Protocentral/protocentral_sensything/docs/images/brain-pipeline.jpg

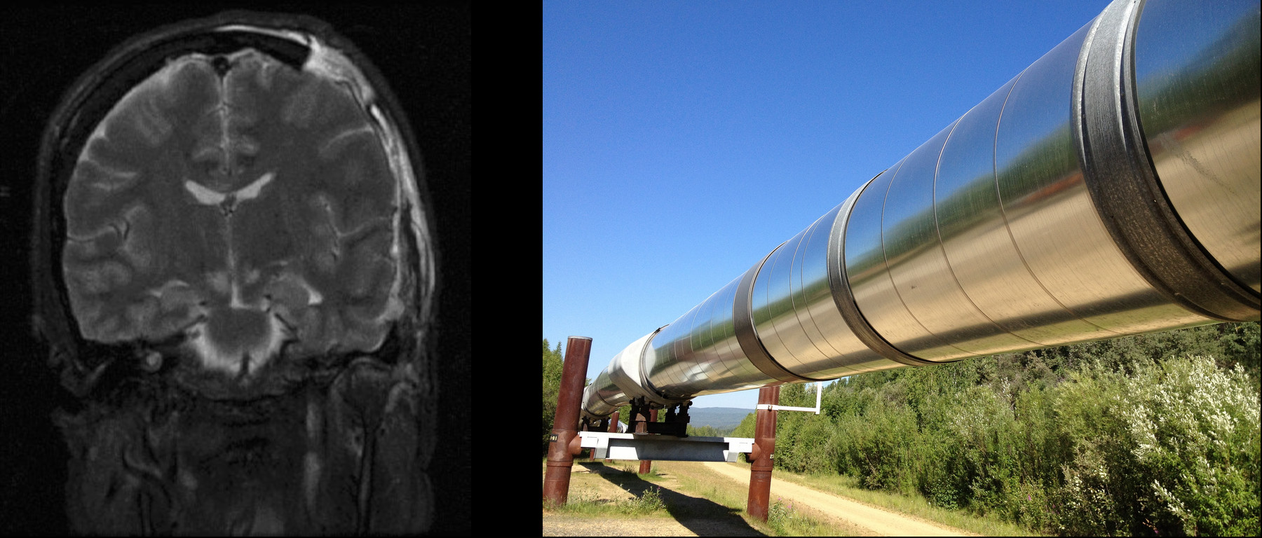
docs/images/brain-pipeline.jpg
