Protocentral/protocentral_sensything/docs/images/curious.jpg

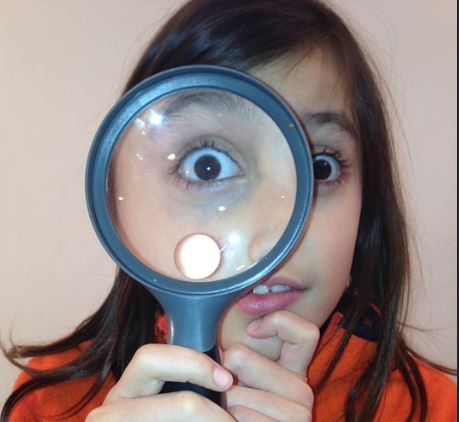
docs/images/curious.jpg
