Protocentral/protocentral_sensything/docs/images/Datalog.JPG

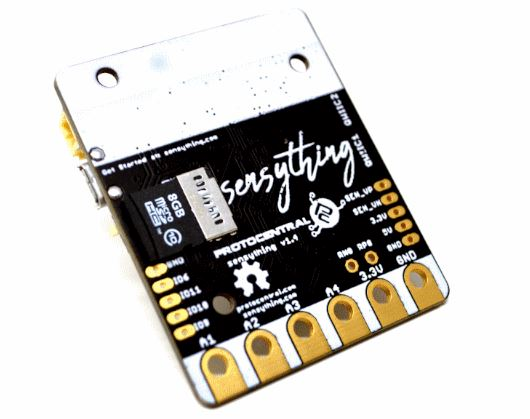
docs/images/Datalog.JPG
