Protocentral/protocentral_sensything/docs/images/Developer mode image.JPG

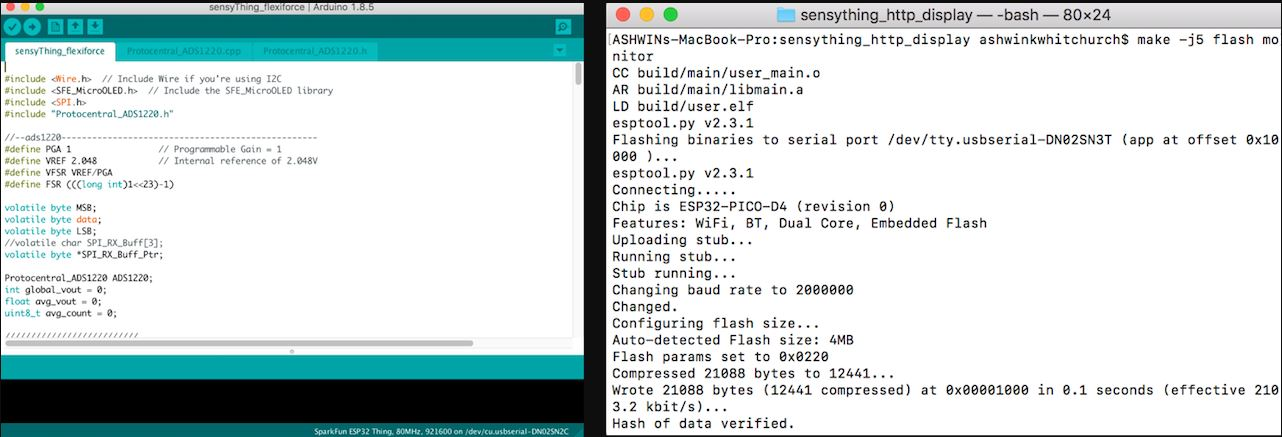
docs/images/Developer mode image.JPG
