Protocentral/protocentral_sensything/docs/images/forest.jpg

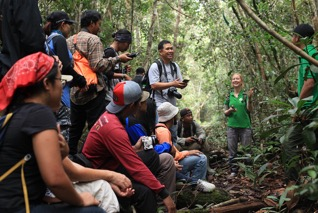
docs/images/forest.jpg
