Protocentral/protocentral_sensything/docs/images/Highlights.jpg

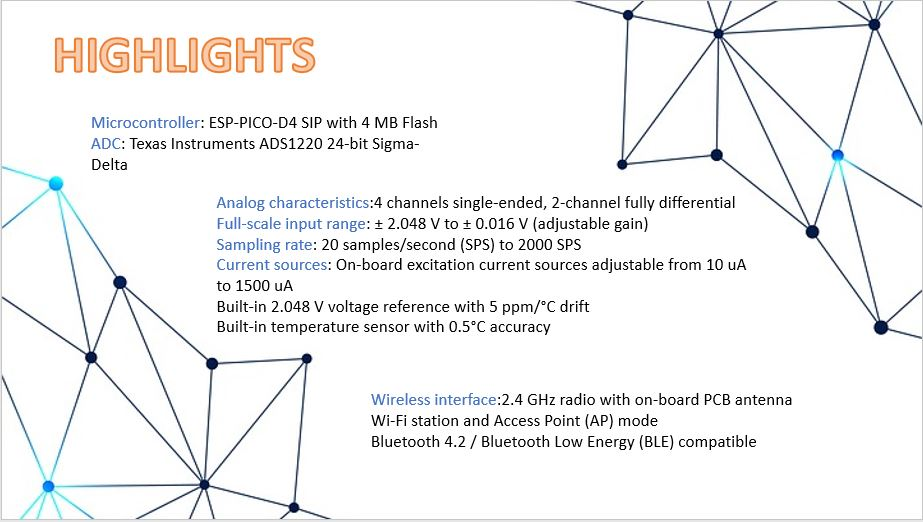
docs/images/Highlights.jpg
