Protocentral/protocentral_sensything/docs/images/openpressure.jpg

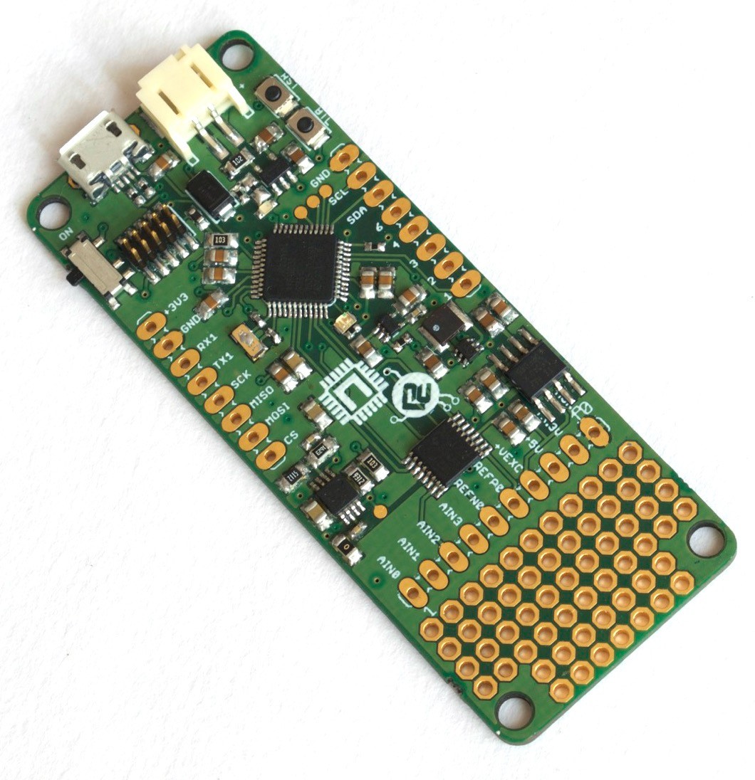
docs/images/openpressure.jpg
