Protocentral/protocentral_sensything/docs/images/protect-the-world.jpg

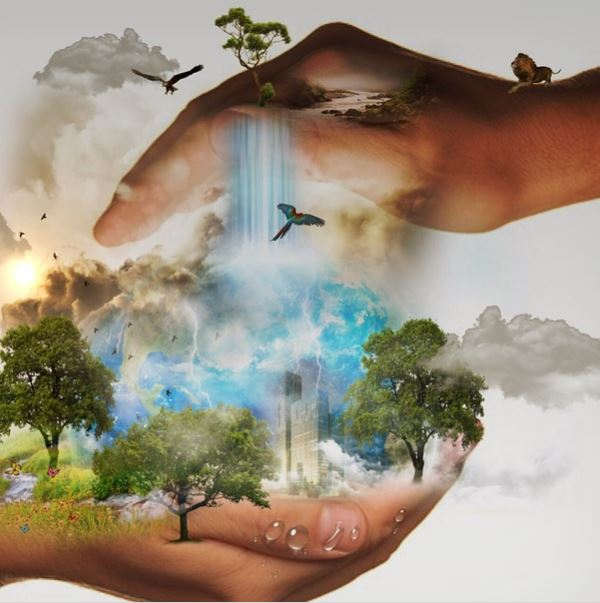
docs/images/protect-the-world.jpg
