Protocentral/protocentral_sensything/docs/images/Read include.png

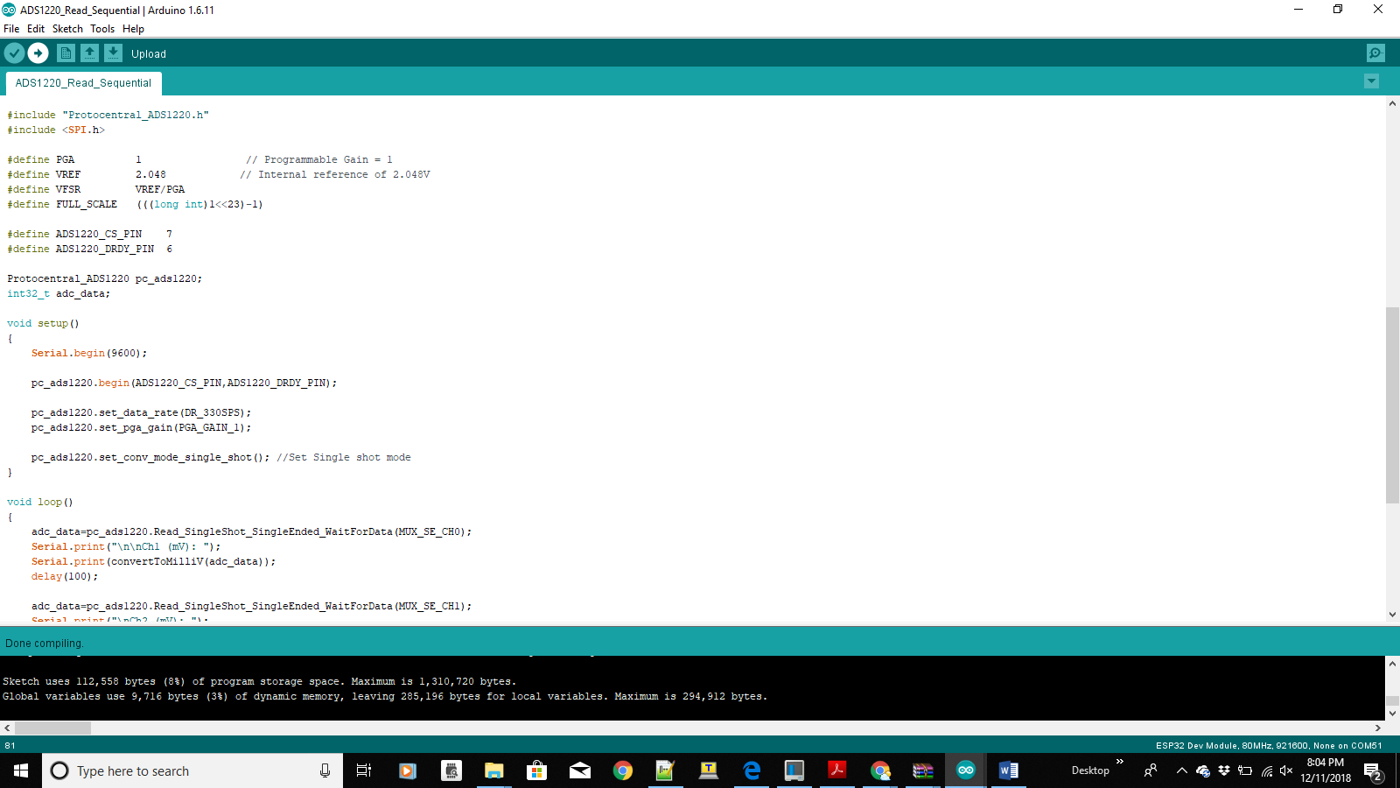
docs/images/Read include.png
