Protocentral/protocentral_sensything/docs/images/Sensything main image.jpg

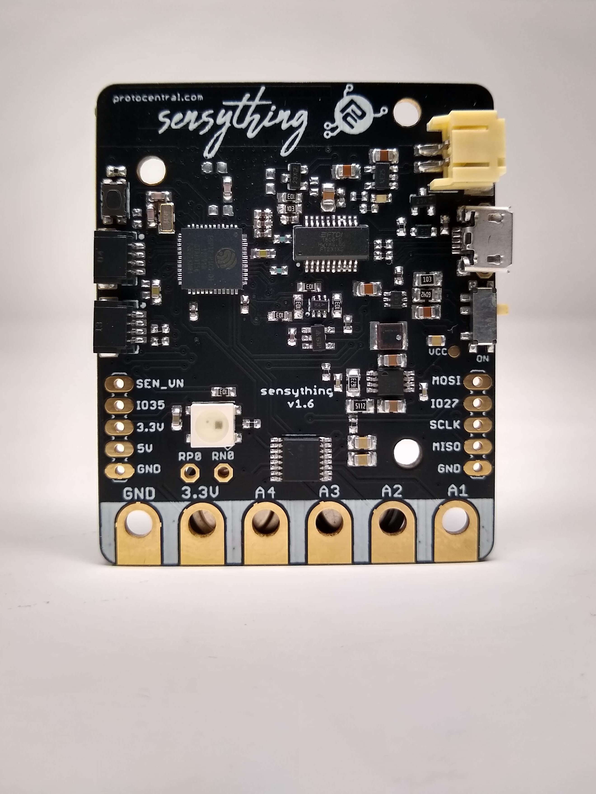
docs/images/Sensything main image.jpg
