Protocentral/protocentral_sensything/docs/images/Sensything main.jpg

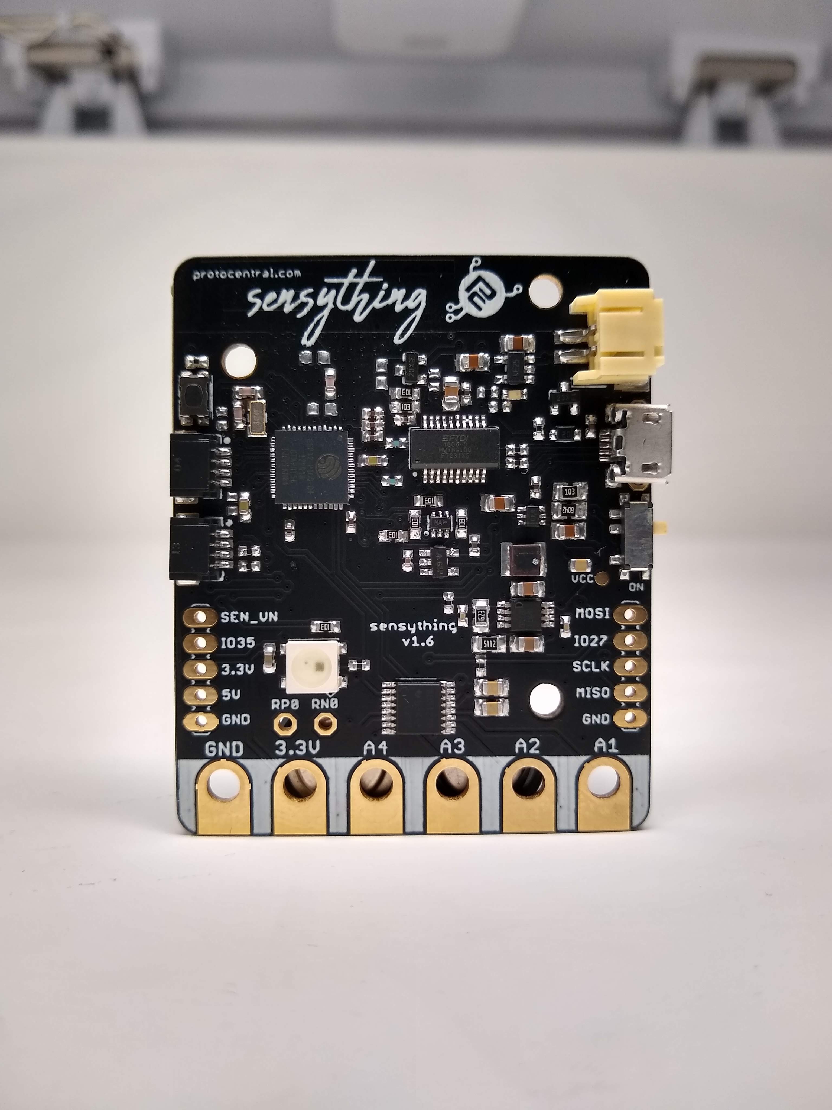
docs/images/Sensything main.jpg
