Protocentral/protocentral_sensything/docs/images/sensything-5-pack.jpg

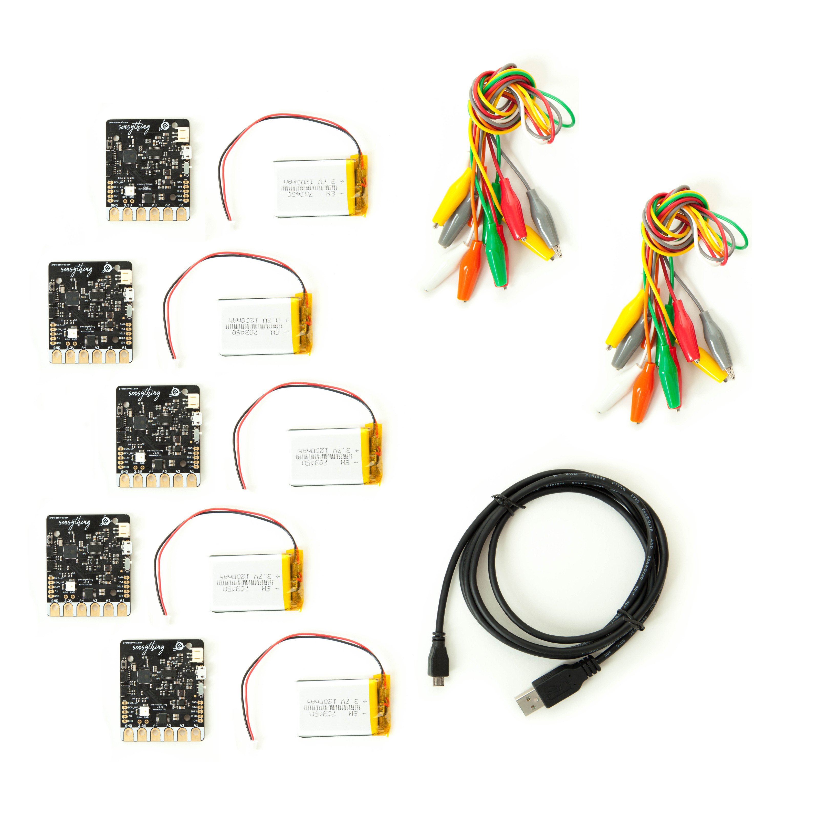
docs/images/sensything-5-pack.jpg
