Protocentral/protocentral_sensything/docs/images/sensything-16.jpg

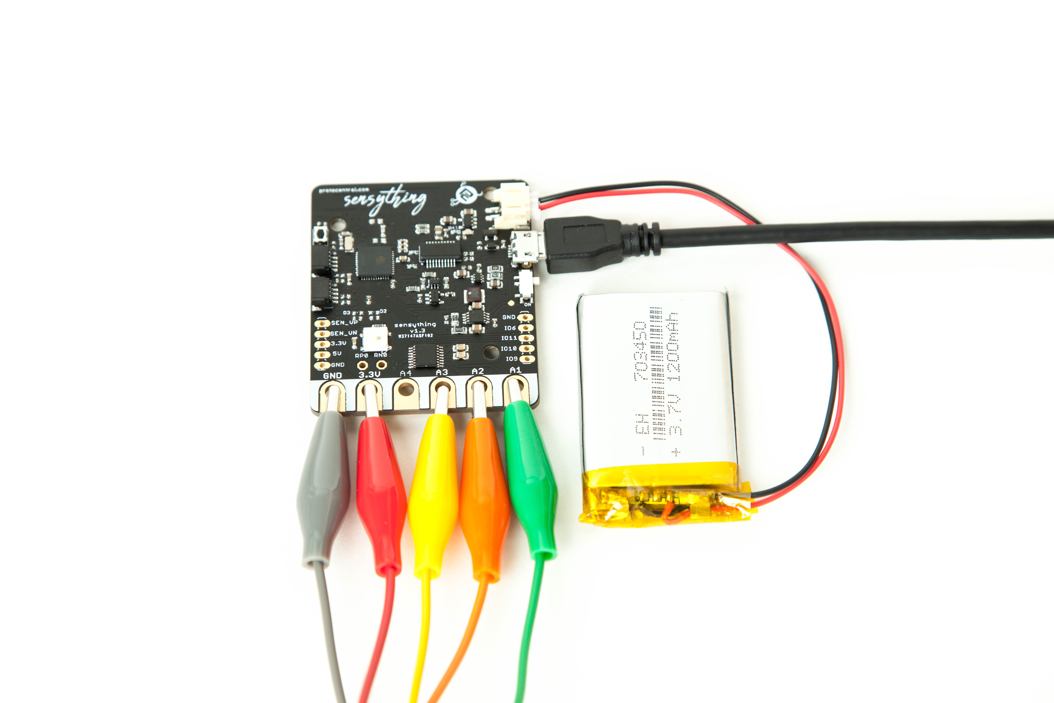
docs/images/sensything-16.jpg
