Protocentral/protocentral_sensything/docs/images/sensything-battery-2.jpg

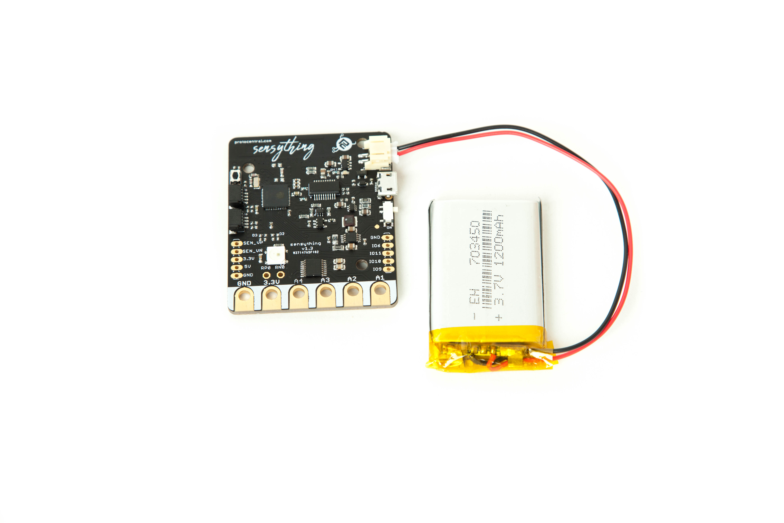
docs/images/sensything-battery-2.jpg
