Protocentral/protocentral_sensything/docs/images/sensything-battery-usb.jpg

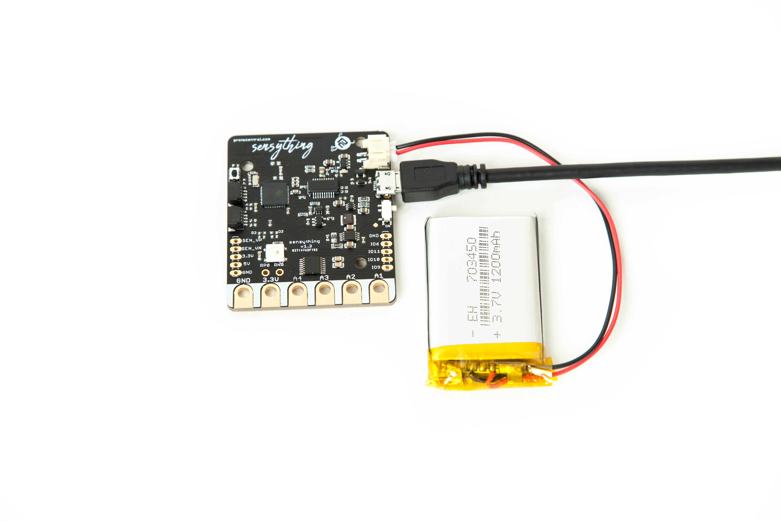
docs/images/sensything-battery-usb.jpg
