Protocentral/protocentral_sensything/docs/images/sensything-battery.jpg

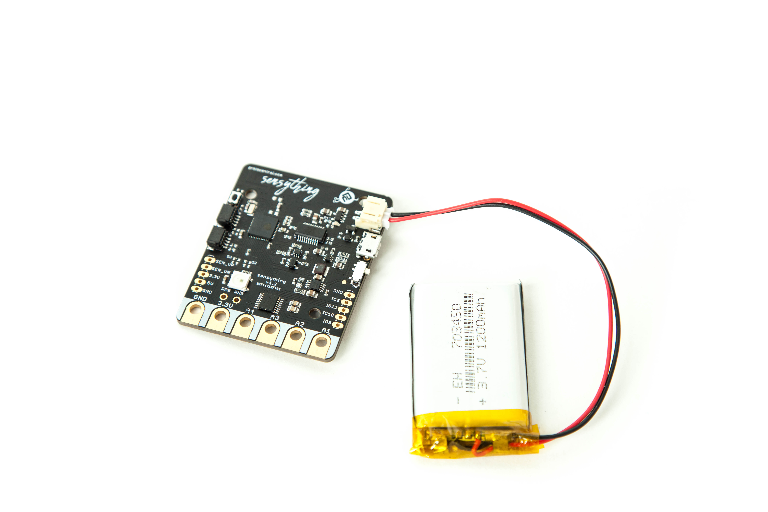
docs/images/sensything-battery.jpg
