Protocentral/protocentral_sensything/docs/images/sensything-bottom.jpg

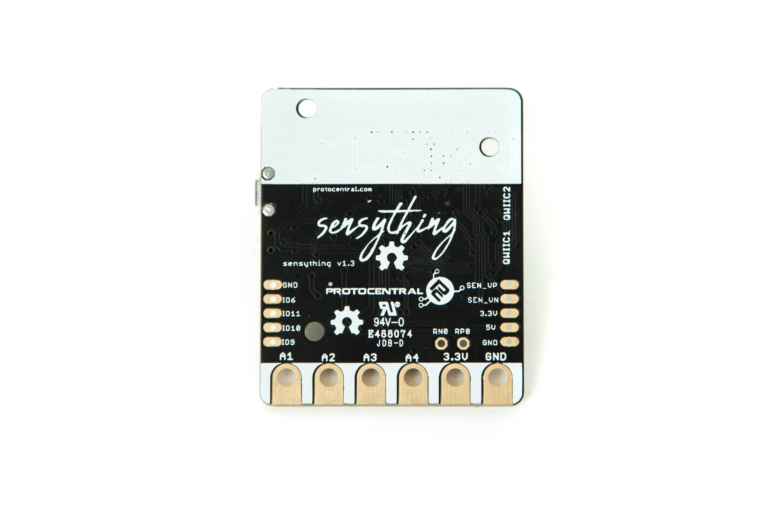
docs/images/sensything-bottom.jpg
