Protocentral/protocentral_sensything/docs/images/sensything-iso.jpg

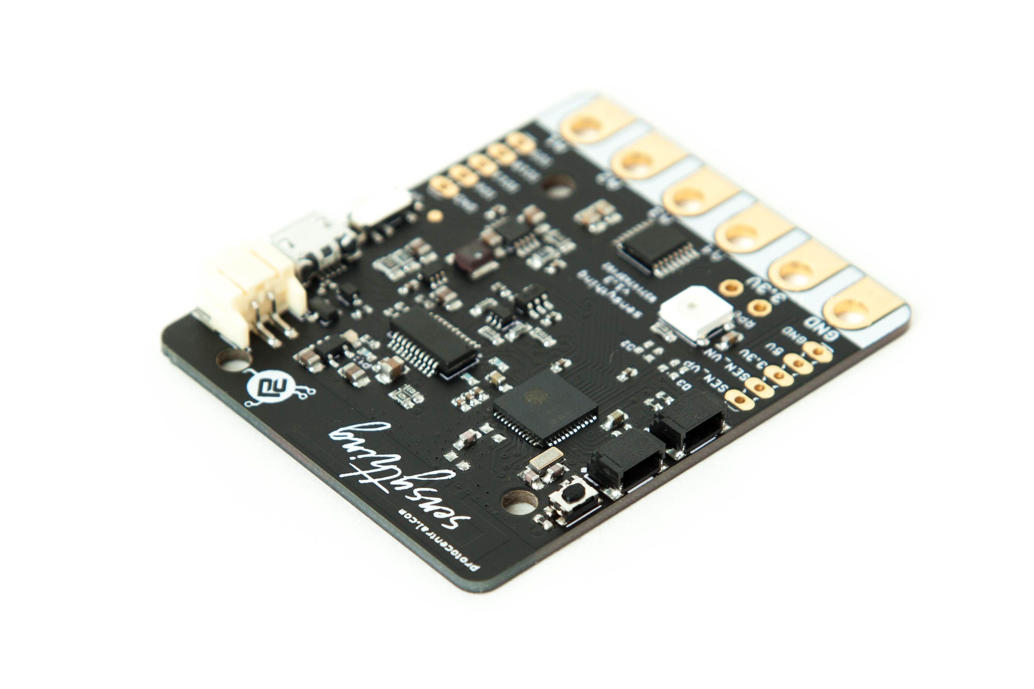
docs/images/sensything-iso.jpg
