Protocentral/protocentral_sensything/docs/images/sensything-microsd.jpg

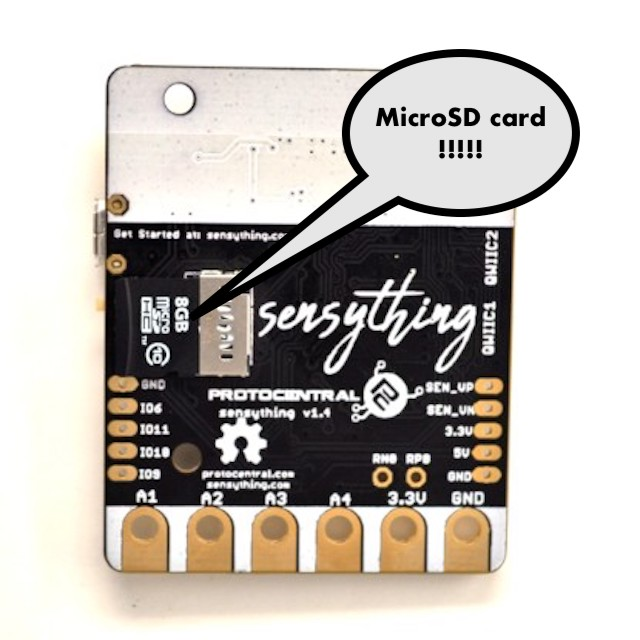
docs/images/sensything-microsd.jpg
