Protocentral/protocentral_sensything/docs/images/sensything-protos.jpg

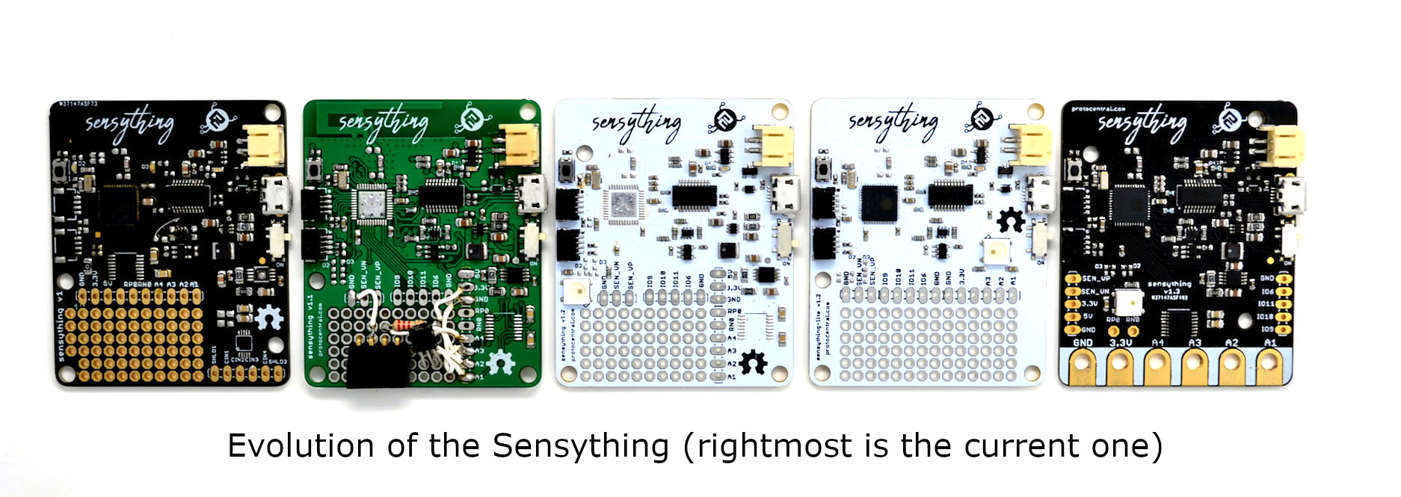
docs/images/sensything-protos.jpg
