Protocentral/protocentral_sensything/docs/images/sensything-shot-sept-26.jpg

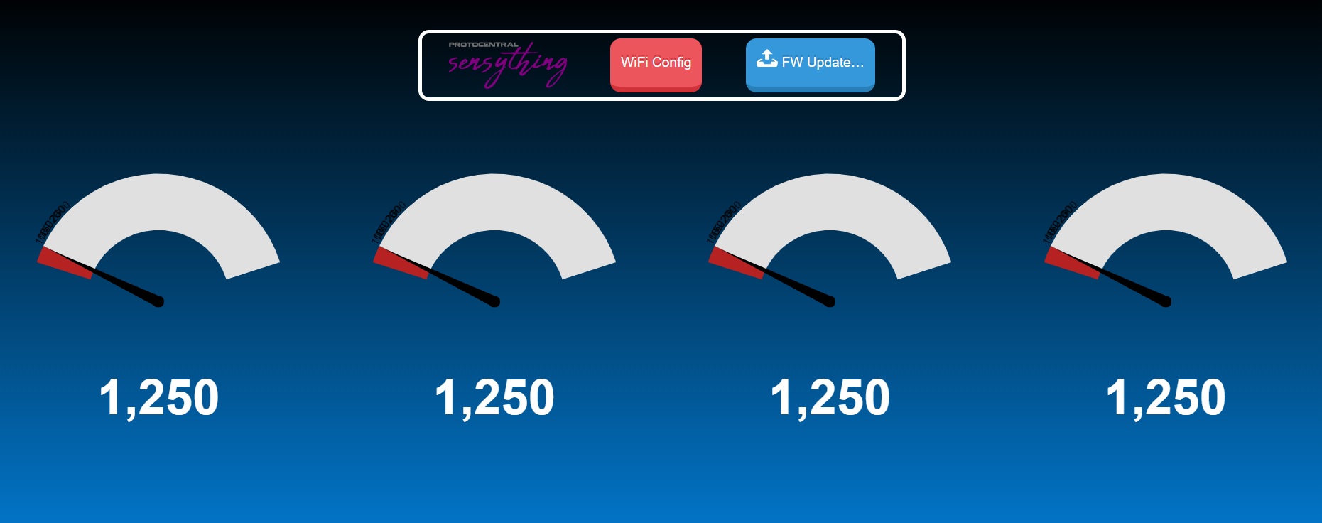
docs/images/sensything-shot-sept-26.jpg
