Protocentral/protocentral_sensything/docs/images/sensything-solo-pledge.jpg

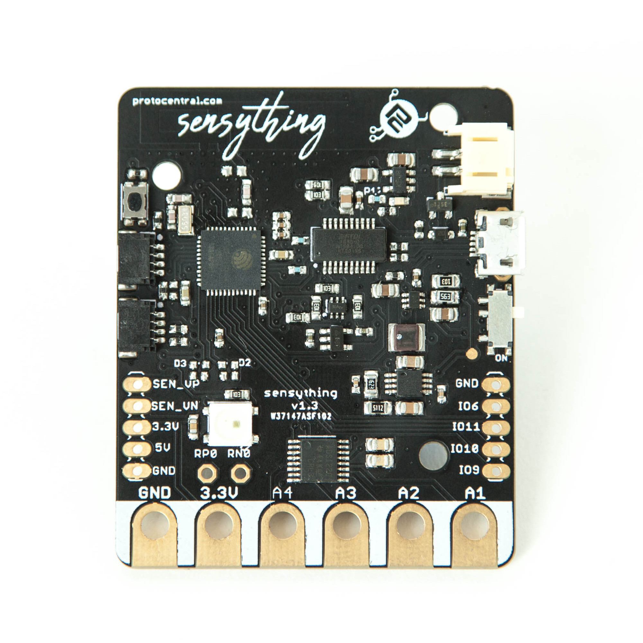
docs/images/sensything-solo-pledge.jpg
