Protocentral/protocentral_sensything/docs/images/sensything-solo.jpg

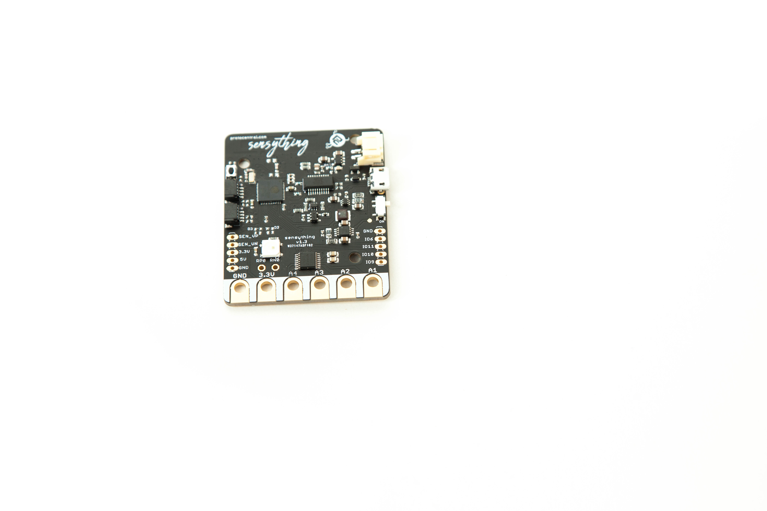
docs/images/sensything-solo.jpg
