Protocentral/protocentral_sensything/docs/images/sensything-top-iso.jpg

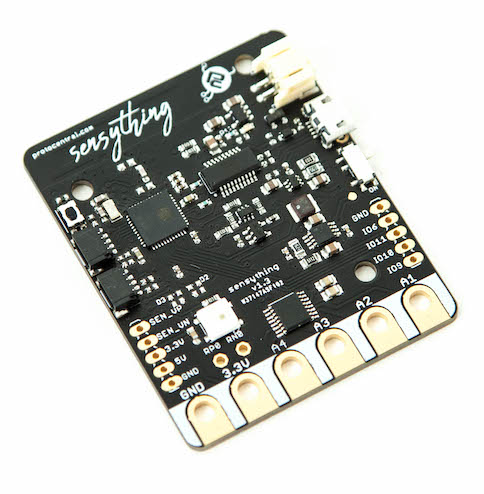
docs/images/sensything-top-iso.jpg
