Protocentral/protocentral_sensything/docs/images/sensything-top-NAMED.jpg

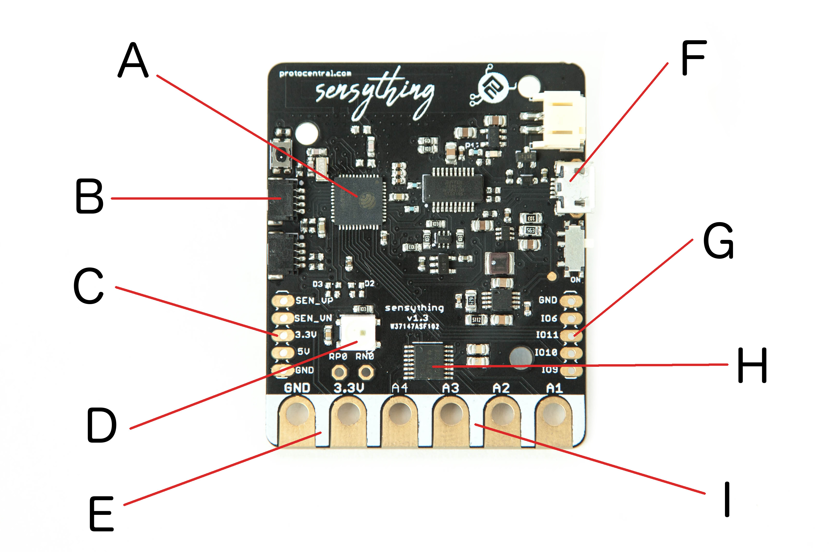
docs/images/sensything-top-NAMED.jpg
