Protocentral/protocentral_sensything/docs/images/sensything-top.jpg

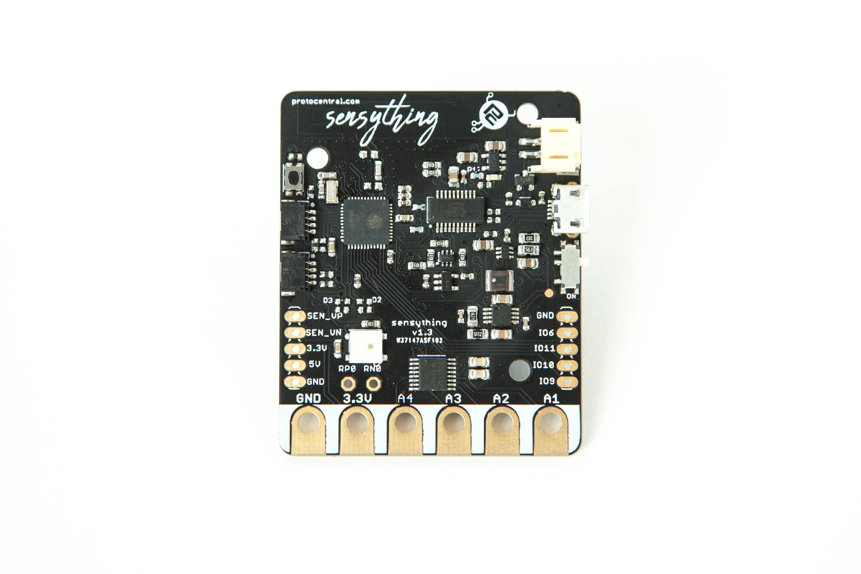
docs/images/sensything-top.jpg
