Protocentral/protocentral_sensything/docs/images/sensything-usb.jpg

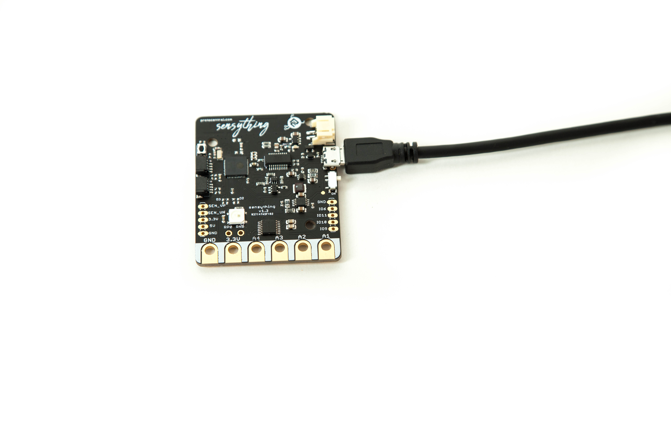
docs/images/sensything-usb.jpg
