Protocentral/protocentral_sensything/docs/images/sensything-with-app-clean.jpg

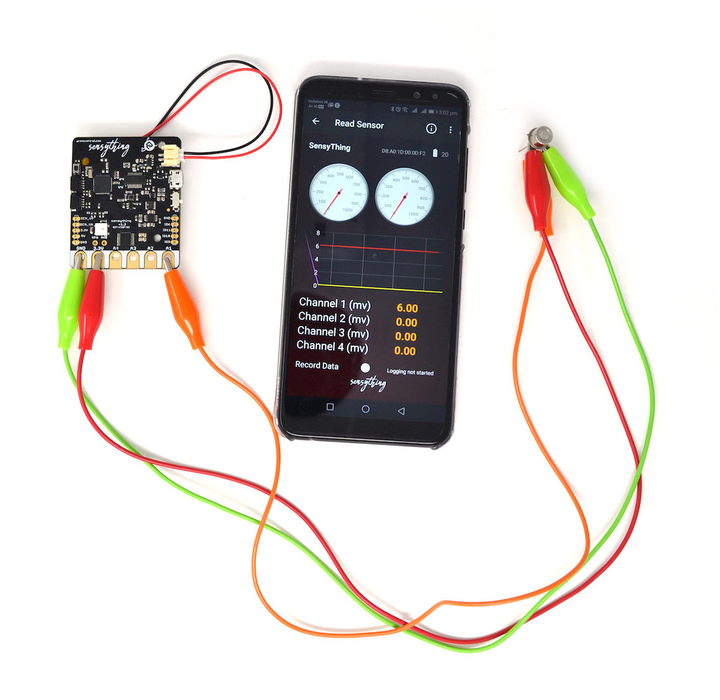
docs/images/sensything-with-app-clean.jpg
