Protocentral/protocentral_sensything/docs/images/sensything-with-app.jpg

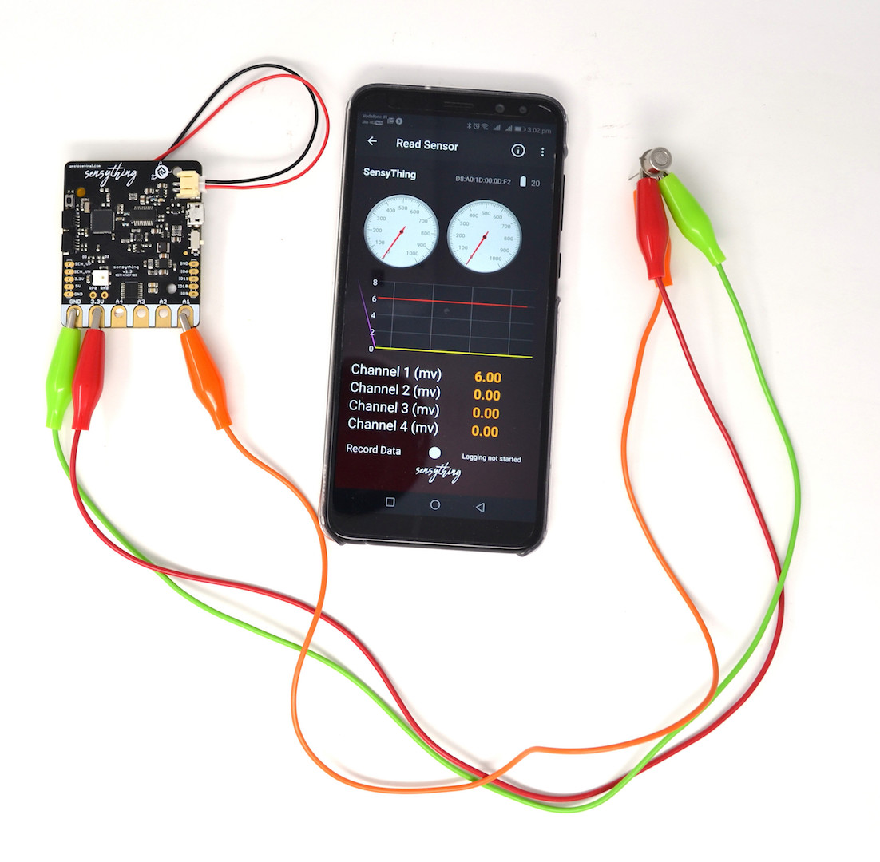
docs/images/sensything-with-app.jpg
