Protocentral/protocentral_sensything/docs/images/sensything-with-sensor.jpg

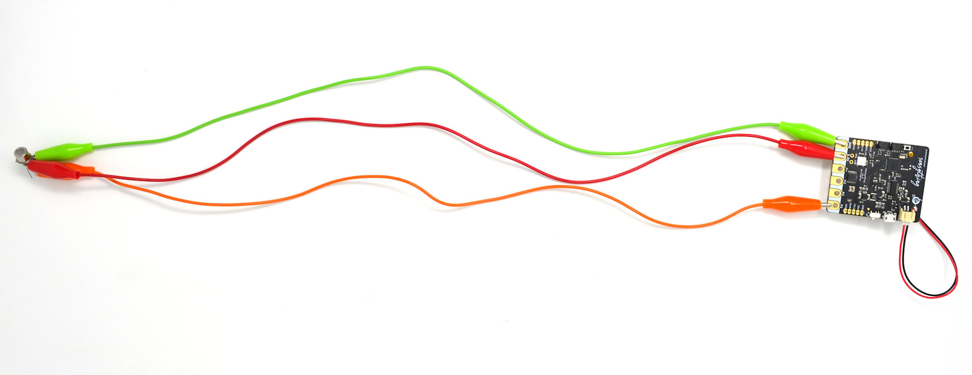
docs/images/sensything-with-sensor.jpg
