Protocentral/protocentral_sensything/docs/images/sensything_prelaunch.jpg

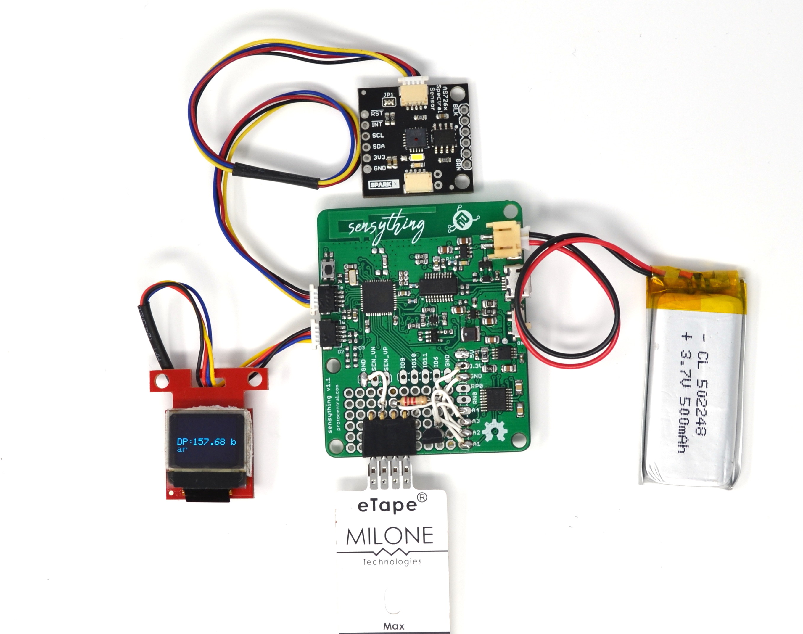
docs/images/sensything_prelaunch.jpg
