Protocentral/protocentral_sensything/docs/images/sensything_qwiic_diagram.png

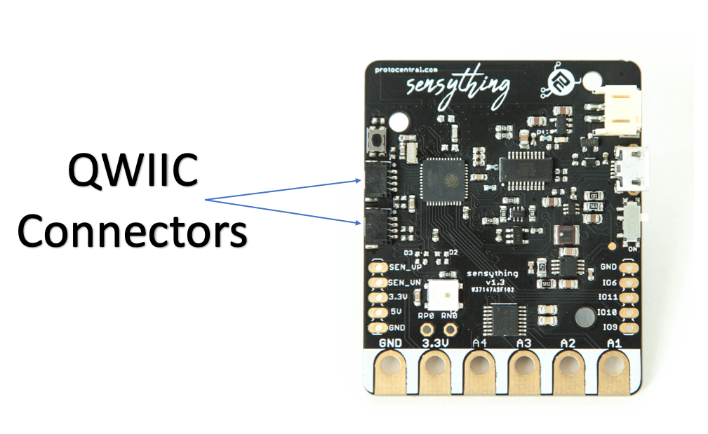
docs/images/sensything_qwiic_diagram.png
