Protocentral/protocentral_sensything/docs/images/signal-adc.png

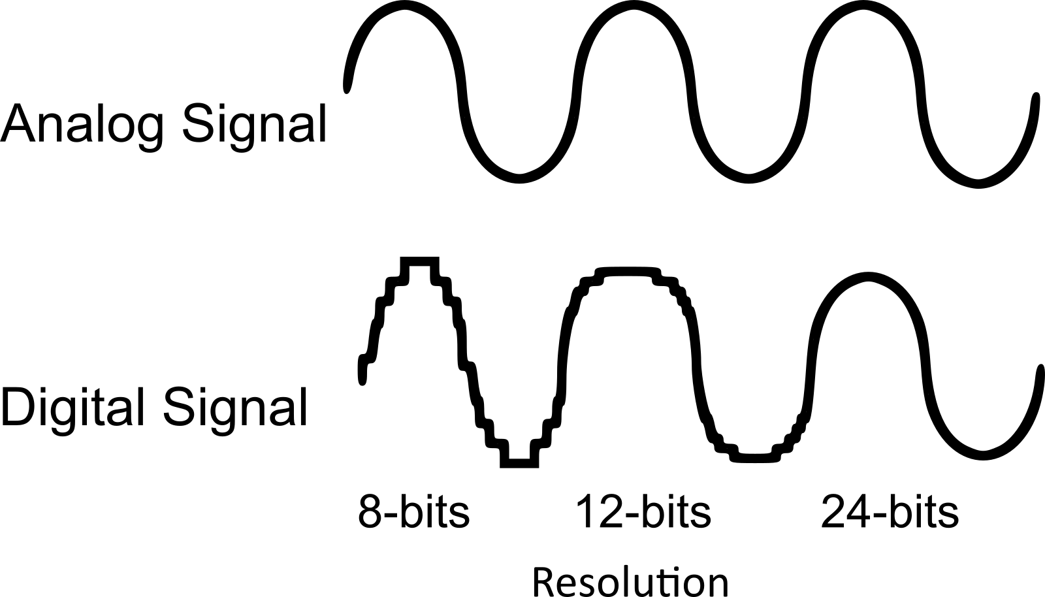
docs/images/signal-adc.png
