Protocentral/protocentral_sensything/docs/images/tree.jpg

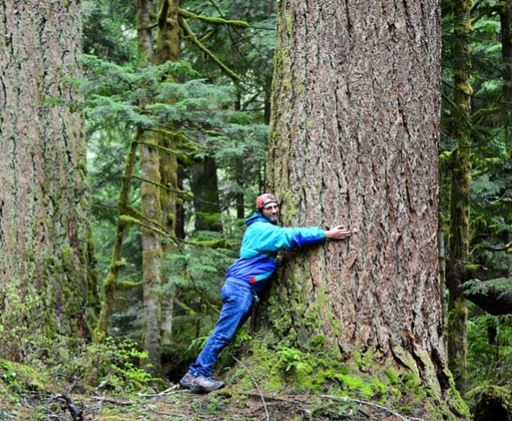
docs/images/tree.jpg
