Protocentral/protocentral_sensything/software/Sensything_esp-idf/Sensything_experiments/Qwiic_Sensors/activity_classifier/components/libesphttpd/util/captdns.c

/* This Source Code Form is subject to the terms of the Mozilla Public
 * License, v. 2.0. If a copy of the MPL was not distributed with this
 * file, You can obtain one at http://mozilla.org/MPL/2.0/. */


/*
This is a 'captive portal' DNS server: it basically replies with a fixed IP (in this case:
the one of the SoftAP interface of this ESP module) for any and all DNS queries. This can
be used to send mobile phones, tablets etc which connect to the ESP in AP mode directly to
the internal webserver.
*/

#include <libesphttpd/esp.h>
#include "esp_log.h"

static const char* TAG = "captdns";

#ifdef FREERTOS

#ifdef ESP32
#include "freertos/FreeRTOS.h"
#include "freertos/task.h"
#include "freertos/queue.h"
#include "tcpip_adapter.h"
#else
#include "FreeRTOS.h"
#include "task.h"
#include "queue.h"
#endif


#include "lwip/sockets.h"
#include "lwip/err.h"
static int sockFd;
#endif


#define DNS_LEN 512

typedef struct __attribute__ ((packed)) {
	uint16_t id;
	uint8_t flags;
	uint8_t rcode;
	uint16_t qdcount;
	uint16_t ancount;
	uint16_t nscount;
	uint16_t arcount;
} DnsHeader;


typedef struct __attribute__ ((packed)) {
	uint8_t len;
	uint8_t data;
} DnsLabel;


typedef struct __attribute__ ((packed)) {
	//before: label
	uint16_t type;
	uint16_t class;
} DnsQuestionFooter;


typedef struct __attribute__ ((packed)) {
	//before: label
	uint16_t type;
	uint16_t class;
	uint32_t ttl;
	uint16_t rdlength;
	//after: rdata
} DnsResourceFooter;

typedef struct __attribute__ ((packed)) {
	uint16_t prio;
	uint16_t weight;
} DnsUriHdr;


#define FLAG_QR (1<<7)
#define FLAG_AA (1<<2)
#define FLAG_TC (1<<1)
#define FLAG_RD (1<<0)

#define QTYPE_A  1
#define QTYPE_NS 2
#define QTYPE_CNAME 5
#define QTYPE_SOA 6
#define QTYPE_WKS 11
#define QTYPE_PTR 12
#define QTYPE_HINFO 13
#define QTYPE_MINFO 14
#define QTYPE_MX 15
#define QTYPE_TXT 16
#define QTYPE_URI 256

#define QCLASS_IN 1
#define QCLASS_ANY 255
#define QCLASS_URI 256


//Function to put unaligned 16-bit network values
static void ICACHE_FLASH_ATTR setn16(void *pp, int16_t n) {
	char *p=pp;
	*p++=(n>>8);
	*p++=(n&0xff);
}

//Function to put unaligned 32-bit network values
static void ICACHE_FLASH_ATTR setn32(void *pp, int32_t n) {
	char *p=pp;
	*p++=(n>>24)&0xff;
	*p++=(n>>16)&0xff;
	*p++=(n>>8)&0xff;
	*p++=(n&0xff);
}

//Parses a label into a C-string containing a dotted
//Returns pointer to start of next fields in packet
static char* ICACHE_FLASH_ATTR labelToStr(char *packet, char *labelPtr, int packetSz, char *res, int resMaxLen) {
	int i, j, k;
	char *endPtr=NULL;
	i=0;
	do {
		if ((*labelPtr&0xC0)==0) {
			j=*labelPtr++; //skip past length
			//Add separator period if there already is data in res
			if (i<resMaxLen && i!=0) res[i++]='.';
			//Copy label to res
			for (k=0; k<j; k++) {
				if ((labelPtr-packet)>packetSz) return NULL;
				if (i<resMaxLen) res[i++]=*labelPtr++;
			}
		} else if ((*labelPtr&0xC0)==0xC0) {
			//Compressed label pointer
			endPtr=labelPtr+2;
			int offset=ntohs(*((uint16_t *)labelPtr))&0x3FFF;
			//Check if offset points to somewhere outside of the packet
			if (offset>packetSz) return NULL;
			labelPtr=&packet[offset];
		}
		//check for out-of-bound-ness
		if ((labelPtr-packet)>packetSz) return NULL;
	} while (*labelPtr!=0);
	res[i]=0; //zero-terminate
	if (endPtr==NULL) endPtr=labelPtr+1;
	return endPtr;
}


//Converts a dotted hostname to the weird label form dns uses.
static char ICACHE_FLASH_ATTR *strToLabel(char *str, char *label, int maxLen) {
	char *len=label; //ptr to len byte
	char *p=label+1; //ptr to next label byte to be written
	while (1) {
		if (*str=='.' || *str==0) {
			*len=((p-len)-1);	//write len of label bit
			len=p;				//pos of len for next part
			p++;				//data ptr is one past len
			if (*str==0) break;	//done
			str++;
		} else {
			*p++=*str++;	//copy byte
//			if ((p-label)>maxLen) return NULL;	//check out of bounds
		}
	}
	*len=0;
	return p; //ptr to first free byte in resp
}


//Receive a DNS packet and maybe send a response back
static char buff[DNS_LEN];
static char reply[DNS_LEN];

#ifndef FREERTOS
static void ICACHE_FLASH_ATTR captdnsRecv(void* arg, char *pusrdata, unsigned short length) {
	struct espconn *conn=(struct espconn *)arg;
#else
static void ICACHE_FLASH_ATTR captdnsRecv(struct sockaddr_in *premote_addr, char *pusrdata, unsigned short length) {
#endif
	int i;
	char *rend=&reply[length];
	char *p=pusrdata;
	DnsHeader *hdr=(DnsHeader*)p;
	DnsHeader *rhdr=(DnsHeader*)&reply[0];
	p+=sizeof(DnsHeader);
    ESP_LOGD(TAG, "DNS packet: id 0x%X flags 0x%X rcode 0x%X qcnt %d ancnt %d nscount %d arcount %d len %d",
		ntohs(hdr->id), hdr->flags, hdr->rcode, ntohs(hdr->qdcount), ntohs(hdr->ancount), ntohs(hdr->nscount), ntohs(hdr->arcount), length);
    //Some sanity checks:
    if (length>DNS_LEN) // Packet is longer than DNS implementation allows
    {
        ESP_LOGD(TAG, "Packet length %d longer than DNS_LEN(%d)", length, DNS_LEN);
        return;
    }
	if (length<sizeof(DnsHeader)) // Packet is too short
    {
        ESP_LOGD(TAG, "Packet length %d shorter than %d", length, sizeof(DnsHeader));
        return;
    }
    // NOTE: We are ok if hdr->arcount is non-zero as these could be extension
    // records, but we don't process them
	if (hdr->ancount || hdr->nscount) //this is a reply, don't know what to do with it
    {
        ESP_LOGD(TAG, "Ignoring reply");
        return;
    }

    if (hdr->flags&FLAG_TC) //truncated, can't use this
    {
        ESP_LOGD(TAG, "Message truncated");
        return;
    }

	//Reply is basically the request plus the needed data
	memcpy(reply, pusrdata, length);
	rhdr->flags|=FLAG_QR;
	for (i=0; i<ntohs(hdr->qdcount); i++) {
		//Grab the labels in the q string
		p=labelToStr(pusrdata, p, length, buff, sizeof(buff));
		if (p==NULL) return;
		DnsQuestionFooter *qf=(DnsQuestionFooter*)p;
		p+=sizeof(DnsQuestionFooter);
		ESP_LOGI(TAG, "DNS: Q (type 0x%X class 0x%X) for %s", ntohs(qf->type), ntohs(qf->class), buff);
		if (ntohs(qf->type)==QTYPE_A) {
			//They want to know the IPv4 address of something.
			//Build the response.
			rend=strToLabel(buff, rend, sizeof(reply)-(rend-reply)); //Add the label
			if (rend==NULL) return;
			DnsResourceFooter *rf=(DnsResourceFooter *)rend;
			rend+=sizeof(DnsResourceFooter);
			setn16(&rf->type, QTYPE_A);
			setn16(&rf->class, QCLASS_IN);
			setn32(&rf->ttl, 0);
			setn16(&rf->rdlength, 4); //IPv4 addr is 4 bytes;
			//Grab the current IP of the softap interface
#ifdef ESP32
            tcpip_adapter_ip_info_t info;
            tcpip_adapter_get_ip_info(TCPIP_ADAPTER_IF_AP, &info);
#else
			struct ip_info info;
			wifi_get_ip_info(SOFTAP_IF, &info);
#endif
			*rend++=ip4_addr1(&info.ip);
			*rend++=ip4_addr2(&info.ip);
			*rend++=ip4_addr3(&info.ip);
			*rend++=ip4_addr4(&info.ip);
			setn16(&rhdr->ancount, ntohs(rhdr->ancount)+1);
			ESP_LOGD(TAG, "Added A rec to resp. Resp len is %d", (rend-reply));
		} else if (ntohs(qf->type)==QTYPE_NS) {
			//Give ns server. Basically can be whatever we want because it'll get resolved to our IP later anyway.
			rend=strToLabel(buff, rend, sizeof(reply)-(rend-reply)); //Add the label
			DnsResourceFooter *rf=(DnsResourceFooter *)rend;
			rend+=sizeof(DnsResourceFooter);
			setn16(&rf->type, QTYPE_NS);
			setn16(&rf->class, QCLASS_IN);
			setn16(&rf->ttl, 0);
			setn16(&rf->rdlength, 4);
			*rend++=2;
			*rend++='n';
			*rend++='s';
			*rend++=0;
			setn16(&rhdr->ancount, ntohs(rhdr->ancount)+1);
			ESP_LOGD(TAG, "Added NS rec to resp. Resp len is %d", (rend-reply));
		} else if (ntohs(qf->type)==QTYPE_URI) {
			//Give uri to us
			rend=strToLabel(buff, rend, sizeof(reply)-(rend-reply)); //Add the label
			DnsResourceFooter *rf=(DnsResourceFooter *)rend;
			rend+=sizeof(DnsResourceFooter);
			DnsUriHdr *uh=(DnsUriHdr *)rend;
			rend+=sizeof(DnsUriHdr);
			setn16(&rf->type, QTYPE_URI);
			setn16(&rf->class, QCLASS_URI);
			setn16(&rf->ttl, 0);
			setn16(&rf->rdlength, 4+16);
			setn16(&uh->prio, 10);
			setn16(&uh->weight, 1);
			memcpy(rend, "http://esp.nonet", 16);
			rend+=16;
			setn16(&rhdr->ancount, ntohs(rhdr->ancount)+1);
			ESP_LOGD(TAG, "Added NS rec to resp. Resp len is %d", (rend-reply));
		}
	}
	//Send the response
#ifndef FREERTOS
	remot_info *remInfo=NULL;
	//Send data to port/ip it came from, not to the ip/port we listen on.
	if (espconn_get_connection_info(conn, &remInfo, 0)==ESPCONN_OK) {
		conn->proto.udp->remote_port=remInfo->remote_port;
		memcpy(conn->proto.udp->remote_ip, remInfo->remote_ip, sizeof(remInfo->remote_ip));
	}
	espconn_sendto(conn, (uint8*)reply, rend-reply);
#else
	sendto(sockFd,(uint8*)reply, rend-reply, 0, (struct sockaddr *)premote_addr, sizeof(struct sockaddr_in));
#endif
}

#ifdef FREERTOS
char udp_msg[DNS_LEN];
static void captdnsTask(void *pvParameters) {
	struct sockaddr_in server_addr;
	int32 ret;
	struct sockaddr_in from;
	socklen_t fromlen;
#ifdef ESP32
    tcpip_adapter_ip_info_t ipconfig;
#else
	struct ip_info ipconfig;
#endif

	memset(&ipconfig, 0, sizeof(ipconfig));
	memset(&server_addr, 0, sizeof(server_addr));
	server_addr.sin_family = AF_INET;
	server_addr.sin_addr.s_addr = INADDR_ANY;
	server_addr.sin_port = htons(53);
	server_addr.sin_len = sizeof(server_addr);

	do {
		sockFd=socket(AF_INET, SOCK_DGRAM, 0);
		if (sockFd==-1) {
			ESP_LOGE(TAG, "captdns_task failed to create sock");
			vTaskDelay(1000/portTICK_RATE_MS);
		}
	} while (sockFd==-1);

	do {
		ret=bind(sockFd, (struct sockaddr *)&server_addr, sizeof(server_addr));
		if (ret!=0) {
			ESP_LOGE(TAG, "captdns_task failed to bind sock");
			vTaskDelay(1000/portTICK_RATE_MS);
		}
	} while (ret!=0);

	ESP_LOGI(TAG, "CaptDNS inited");
	while(1) {
		memset(&from, 0, sizeof(from));
		fromlen=sizeof(struct sockaddr_in);
		ret=recvfrom(sockFd, (uint8_t *)udp_msg, DNS_LEN, 0,(struct sockaddr *)&from,(socklen_t *)&fromlen);
		if (ret>0) captdnsRecv(&from,udp_msg,ret);
	}

	close(sockFd);
	vTaskDelete(NULL);
}

void captdnsInit(void) {
#ifdef ESP32
	xTaskCreate(captdnsTask, (const char *)"captdns_task", 3000, NULL, 3, NULL);
#else
	xTaskCreate(captdnsTask, (const signed char *)"captdns_task", 1200, NULL, 3, NULL);
#endif
}

#else

void ICACHE_FLASH_ATTR captdnsInit(void) {
	static struct espconn conn;
	static esp_udp udpconn;
	conn.type=ESPCONN_UDP;
	conn.proto.udp=&udpconn;
	conn.proto.udp->local_port = 53;
	espconn_regist_recvcb(&conn, captdnsRecv);
	espconn_create(&conn);
}

#endif
